constral/2-bit_alu/logi_wrong.png

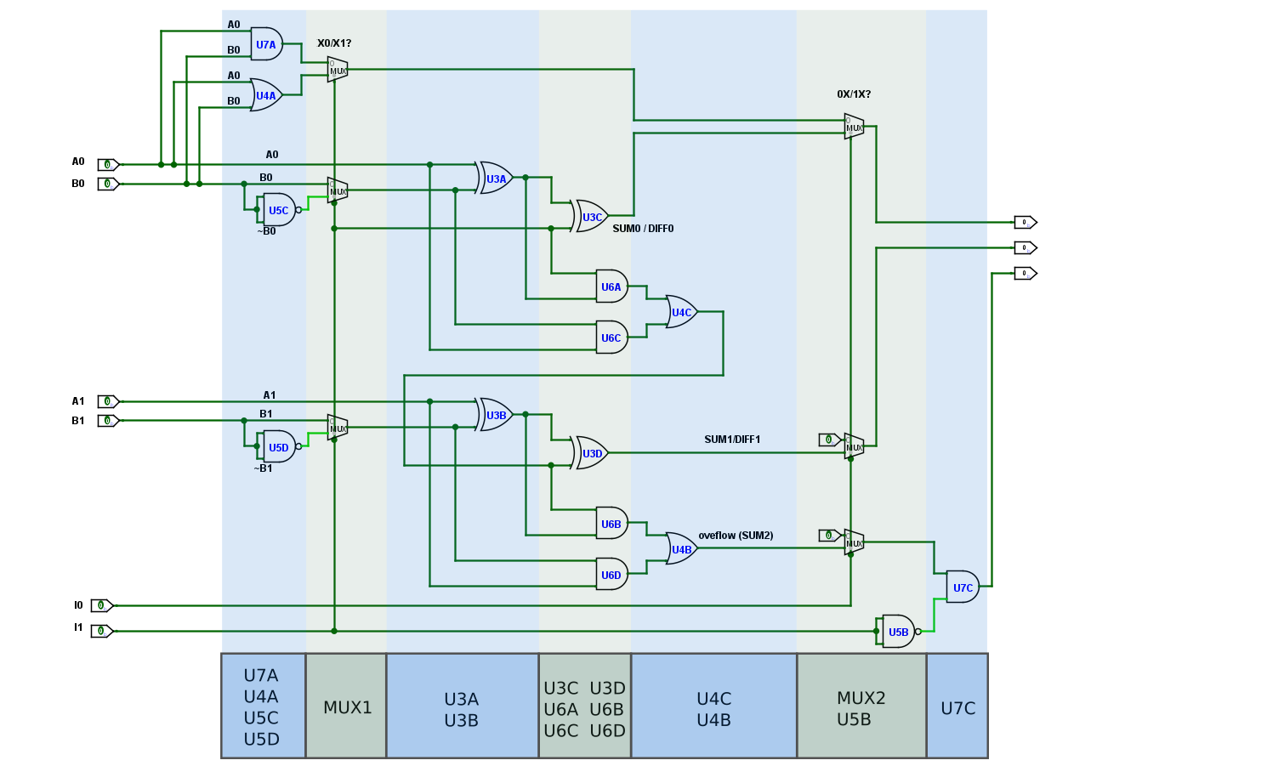
logi_wrong.png
